snopf/snopf/src/avr/eeprom_access.c

// Copyright (c) 2020 Hajo Kortmann <hajo.kortmann@gmx.de>
// License: GNU GPL v2 (see License.txt)

#include "eeprom_access.h"

EEMEM struct EEPROM_LAYOUT eeprom_layout = {
    .dummy = 0x00,
    
    // Address 0x01
    .secret = {
        0x00, 0x00, 0x00, 0x00, 0x00, 0x00, 0x00, 0x00, 
        0x00, 0x00, 0x00, 0x00, 0x00, 0x00, 0x00, 0x00,
        0x00, 0x00, 0x00, 0x00, 0x00, 0x00, 0x00, 0x00, 
        0x00, 0x00, 0x00, 0x00, 0x00, 0x00, 0x00, 0x00},
    
    // Address 0x21
    .sha256_k = {
    0x428a2f98, 0x71374491, 0xb5c0fbcf, 0xe9b5dba5, 0x3956c25b, 0x59f111f1,
    0x923f82a4, 0xab1c5ed5, 0xd807aa98, 0x12835b01, 0x243185be, 0x550c7dc3,
    0x72be5d74, 0x80deb1fe, 0x9bdc06a7, 0xc19bf174, 0xe49b69c1, 0xefbe4786,
    0x0fc19dc6, 0x240ca1cc, 0x2de92c6f, 0x4a7484aa, 0x5cb0a9dc, 0x76f988da,
    0x983e5152, 0xa831c66d, 0xb00327c8, 0xbf597fc7, 0xc6e00bf3, 0xd5a79147,
    0x06ca6351, 0x14292967, 0x27b70a85, 0x2e1b2138, 0x4d2c6dfc, 0x53380d13,
    0x650a7354, 0x766a0abb, 0x81c2c92e, 0x92722c85, 0xa2bfe8a1, 0xa81a664b,
    0xc24b8b70, 0xc76c51a3, 0xd192e819, 0xd6990624, 0xf40e3585, 0x106aa070,
    0x19a4c116, 0x1e376c08, 0x2748774c, 0x34b0bcb5, 0x391c0cb3, 0x4ed8aa4a,
    0x5b9cca4f, 0x682e6ff3, 0x748f82ee, 0x78a5636f, 0x84c87814, 0x8cc70208,
    0x90befffa, 0xa4506ceb, 0xbef9a3f7, 0xc67178f2},
    
    // Address 0x121
    .sha256_h0 = {
        0x6a09e667, 0xbb67ae85, 0x3c6ef372, 0xa54ff53a,
        0x510e527f, 0x9b05688c, 0x1f83d9ab, 0x5be0cd19},

    // Address 0x141, begin of unprotected space
    .kb_delay = 20,
     
    // Address 0x142
    // Keycodes, first byte modifier, second byte key
    .keycodes = {
        // a..r
        {0x00, 0x04}, {0x00, 0x05}, {0x00, 0x06},
        {0x00, 0x07}, {0x00, 0x08}, {0x00, 0x09},
        {0x00, 0x0a}, {0x00, 0x0b}, {0x00, 0x0c},
        {0x00, 0x0d}, {0x00, 0x0e}, {0x00, 0x0f},
        {0x00, 0x10}, {0x00, 0x11}, {0x00, 0x12},
        {0x00, 0x13}, {0x00, 0x14}, {0x00, 0x15},
        // A..R
        {0x02, 0x04}, {0x02, 0x05}, {0x02, 0x06},
        {0x02, 0x07}, {0x02, 0x08}, {0x02, 0x09},
        {0x02, 0x0a}, {0x02, 0x0b}, {0x02, 0x0c},
        {0x02, 0x0d}, {0x02, 0x0e}, {0x02, 0x0f},
        {0x02, 0x10}, {0x02, 0x11}, {0x02, 0x12},
        {0x02, 0x13}, {0x02, 0x14}, {0x02, 0x15},
        // 0..9
        {0x00, 0x27}, {0x00, 0x1e}, {0x00, 0x1f},
        {0x00, 0x20}, {0x00, 0x21}, {0x00, 0x22},
        {0x00, 0x23}, {0x00, 0x24}, {0x00, 0x25},
        {0x00, 0x26},
        // -, @, ! 
        {0x00, 0x2d}, {0x02, 0x1f}, {0x02, 0x1e},
        // ?, $, *
        {0x02, 0x38}, {0x02, 0x21}, {0x02, 0x25},
        // +, =, &
        {0x02, 0x2e}, {0x00, 0x2e}, {0x02, 0x24},
        // #, [, ]
        {0x02, 0x20}, {0x00, 0x2f}, {0x00, 0x30},
        // (, ), .
        {0x02, 0x26}, {0x02, 0x27}, {0x00, 0x37},
        // :, >, <
        {0x02, 0x33}, {0x02, 0x36}, {0x02, 0x37}
    }
};

void ee_access_set_secret(const uint8_t secret[32])
{
    eeprom_update_block(secret, eeprom_layout.secret, 32);
}

void ee_access_set_keyboard_delay(uint8_t delay)
{
    eeprom_update_byte(&eeprom_layout.kb_delay, delay);
}

void ee_access_set_keyboard_codes(const uint8_t keyboard_codes[128])
{
    eeprom_update_block(keyboard_codes, (uint8_t*)eeprom_layout.keycodes, 128);
}

int8_t ee_access_get_key_modifier(uint8_t index, uint8_t* modifier)
{
    if (index >= 64) {
        return 0;
    }
    *modifier = eeprom_read_byte(&(eeprom_layout.keycodes[index][0]));
    return 1;
}

int8_t ee_access_get_key_code(uint8_t index, uint8_t* keycode)
{
    if (index >= 64) {
        return 0;
    }
    *keycode = eeprom_read_byte(&(eeprom_layout.keycodes[index][1]));
    return 1;
}
