snopf/snopf/src/host/pc/resources_rc.py

# Resource object code (Python 3)
# Created by: object code
# Created by: The Resource Compiler for Qt version 5.15.0
# WARNING! All changes made in this file will be lost!

from PySide2 import QtCore

qt_resource_data = b"\
\x00\x00\x09\xb5\
\x00\
\x00\x22\x03x\x9c\xcdZYo\x1b\xc9\x11~\xcf\xaf\xe8\
0/6\xc0\xa3\xefC\x90v\x11\xd3^\xc3\x80\x9c5\
b;\xc1\xfa\xc5\xa0\xc9\xb1\xc4,/p\xa8#\xff>\
_U\xf7\x0cG\x8a\xec\x95L)\xc8\x03\xd5U\xdd\xd5\
U\xd5_\xd5\xd4T\x0ft\xfc\xf3\xf5r!.\xabm\
=_\xafNzj({\xa2ZM\xd7\xb3\xf9\xea\xec\
\xa4\xf7\xf1\xc3/\x83\xd8\xfb\xf9\xa7?\x1d\xff\xf9\xe5\xaf\
\xe3\x0f\xbf\xbd{%\xea\xcb3\xf1\xee\xe3\x8b\xd37c\
\xd1\x1b\x8cF\xff4\xe3\xd1\xe8\xe5\x87\x97\xe2\xfd?^\
\x0b5T\xa3\xd1\xab\xbf\xf5D\xef|\xb7\xdb\x1c\x8dF\
WWW\xc3+3\x5co\xcfF\xaf\xb7\x93\xcd\xf9|\
Z\x8f 8\x22Al\x1aA\x99R\xc3\xd9n\xd6\x83\
\x09\xd2\xdcqD\xf7\xc4\xd5|\xb6;?\xe9%;\x0c\
f\xb9\xec\x89\xf3j~v\xbe\xebL\x5c\xce\xab\xab\x17\
\xeb\xeb\x93\x9e\x0b\xde\x0a%\x95\xb2\x22\xd9`\xf8OO\
l\xb6U]m/\xab\xbf\xd6\x9bj\xba\xfb\xfbd7\
_\x9f\xf4\xae\xdf\xceg\xbf\xe1\xd7\x13_\xe7\x8b\xc5`\
{\xb1\xa8Nz\xd5e\xb5Z\xcf0W\xef\xb6\xeb\xdf\
\xabA\xb1\xac\xe3Pk\xdd\xce.\xe6\xab\xea_\xeb9\
\xdc\xdb\xae/V\x90\x06v\xab\xfa\xe4\x8e\xd3j)%\
\x9d\xae\x88\x1c\xad\xd7\xebV\x0c3\xc3\xf5\x06\xf6\xbe~\
\x9dO+\x16\x87\xe4\xa8\xba\xde\xac\xb7\xbbf\xc35l\
\xfd~\x97f\x95R\x1a\xf1j#\xca\xa7\x5c\xed\xe8t\
\xabvG}\xb1\x1aN\xd7\xcb\x11\x8b\x8c\xea\xddd\x9b\
\xcd\x8d\xba\xd2\x8d\x86z9_|\xe3\x14j\xf4\xfe\xed\
\x9bS-G\x8d\xecd5_\x9e\xf4.\xb6\xab\xa3\xf5\
\xa4\x9e\xd7G\xab\xc9\xb2\xaa\x8fv\xd3#:\xd2l=\
\xbdXB\xfb\xd1^\x96\x0d\x1dq^a\xf2\xa8\xdeL\
\xa6\xc0\xbb\x89\x0c\xe2.\x8eg\xd5\xd7ZL\x17\x93\x1a\
P\x8e\x17\xf3\xcd\xbb\xc9\xee\xfc5\x10\xde\xd0\xaa8\x9e\
\x96)1\x9f\x95\x8d\xc5\xfd\xcf\xb4\xf2y\x83\xa5\x9eh\
\x84>\xae\xe6;\xa8\xb9\x80\xf6\xf7d\xea\xd7\xd5\xc7\x9a\
\xad@\xd1\x16I J\xb2\xf4\xc4\xbf\x91d\x940\x9d\
4\xa3\x9c\xd9\xe7\x18\xb8\x11;0j\x94\xdf\xd7\x9d\xcf\
\xf5\xf9\x96\x03\xf40\xaf\xc8|\xf6J\x9b\x8eW\xceu\
\xbd\x02\xf7\xdf^\x1d\x8f\x08\xc3\xdbX~\xa8\xaew\xef\
\xcf'\x9b\xea\xcdjV]g0\xcf\x04R\xf1\xa8^\
\xccg\x88\xc2|\xa6z\xcc\xcfg\xc8\xedzG3\x06\
\xe7\xb2\xf89\xfc<~\x01\xbf\x88_\xc2OI\xfa\xa3\
\xe8\x8ff/\xee\xb6\xfbj\xf9\xa5\x9a\xcd\xaa\xd9\x8b\x8b\
\xc5\xa2\xda\x8d\xcf'\xdb\xba1N\x98}\xe1\xe9\xc1\x14\
\xf3\x83]\xb5\xdc,&\xbbj\xe0\x82q\xbe'v\xdb\
\xc9\xaa\xfe\xba\xde\x22\xc5\xea\xe9dQ=\x93C<I\
6F\x1d\x95v\xfd\xc1\x0d\xf6yA\x90 \x17P\xfc\
V\xb8(\xfb\x08\xa9\x12\xa7B)o\xfa.(\x9e\x93\
b`[\x86\x05>5(\x9e\xdd\xc73{\xb0g\x11\
fud\xbfL\xc84S\x12+\xb2Y\xbd\xbfS\xc8\
\x11{8\x5c*X\x18?\x15^\xea~0\x89ye\
\xa3\x12\xca:\xdf\xceH\xf1I@\xd6\xb8\xc8S\xa7\xc2\
\xc8\xd4W\xc6z\xe1]\xcaR\xcd\xda\x83\x0e`\xf4\xc1\
\x07\xd0R\xb9\xe2\x94\xd2\xc1\xc3\xd5\xa0\x08S\xa5\xbd\xec\
;k\xd8\xfffL\xc6\xe7\x05\x22H.\x1fU7\x87\
n\x95=\xe4\x14R\x86\x83O!\xfb\x03-\xc6b@\
\x1e\x89\x81\xf2}\x1d\xc4\x00\xfbL \xb0\x11\x09\xe7\x03\
\xd6\xb5\xd7\xfd\xa8\x8d\xd0p39]F\x9b\xc7\x90\x84\
\xd6\xb1\x9f\x12\xe6\x9d\xcb\xa3\xb7y\x040)I\xa1c\
\xea\xa7\x18\x84Q\x80 )a\x8c\xc2\x98`\x01\x00\xa0\
\xe6\x90\xb1\x98\xa7lBB\xd8(B\xd0X\xb2ID\
\xe3Ah+\x22\xf0\xe3\x99\xb1\x88\x10V\x12x%I\
\x84v\x22i\x12\x97\x1eK0\x09\xf7\xa3q\xfd\xe8\x0d\
\xf4\xc8~\x88V\x04\x8f\x84\x89\xe0\xe1BP^\xb8\x84\
\xf0`\xfe\x14\x12\xb6\xafq\xb81S*!B\xce\xf4\
\x95\x87\x0f\x0a\xda9\xc4A\xd3\x93C\xa6)z8\x91\
OP\x874\x84\x974XE\x83\x83-\x15\xa2\xb0.\
\xf4q\x1eJ\x0d\x001\xc0\xca\x18y\xad\xfb\x03\x852\
\xa6\xa0t\x80\xd0Cg\x1e\x8d\xccc\xca\xeb\x917@\
\xc6S(\xfa\x03\xc0M\x83\xc9\x03\xfc\x1c\xd0~\x93C\
\xf7\xb0|9\xbc\x96\xe8\x08\x19CX\xa9\xa8\x99\xa2\xe3\
\x18$?\x90s@@\x03J\x00\x809\xaca\xb0\xa8\
|\x18\x1c\xc2\x86\xdc\xf0\x00\x1e\xfb\x80\x1a\x15I\xc4\x19\
\xfb).\xc0L[\x99\xc7dx4H\xa9`\x81\x8e\
\xf5}\xcfq2\x90t2\xc2\xb6\x09\xa1o\xad\x15&\
a\xc4K\xc1B\xd6*\xd9\x94^\xb8\xc4\x88sM!\
d\x119\xe4\x90\x22o\xb5N\x0d\x15TC!\xe5\xb0\
'\x16J\xc6\xc0\x0f5\xe8\xe4\x1d)bR\xa3\xd8h\
8\x8f\x94\xa3g\x19\x0f\x04G\xd8\x22\xae\x96\x9e\x11\x93\
\x10\x11\x8f\xd4\x8e\x8cK\x83\xd4\xfd#\x94|H\x87\x17\
{eP\x84\xc6\xc2\x1b\x8d\xd1\xe2\xb9\xc3cj\x22\xe5\
\xb3\xe2\xc7Q#\xaf\x91\xed\x8c\x1b\x8d\x8e\x1eSM\x98\
\x9b\xfc\xb8\x02;\x96\x97H5\xda\x0f\x8c$\xab\x03B\
\x96\xf53\x91R\x99\xc1\xba\xcfBJ[\x97\xf7\xa1*\
\x1b\xd6\xa4\xac\x0cP\xad3A\xb6\x98\xb0x\xe4Y\x86\
\xbc\xc9\xdb\xe0\x1ekrY\xb5,'\xb9?|Q\xeb\
\xc3_K\x94mxz\xa9\xe4\x05\xc3\x94\xc6\x1b\xc7\xa2\
n(\xa4\xaf3\x8e:}\xd4\x0dO\x09\xef\x91\xd4\x18\
\x02\x0eL\x03\x0a\x07-F\x97X8\x11\xc0\xd8\x9c\xbc\
ae)&VO\xa3U)\x8f\xe8\x09h\xddQ=\
D\x02;\xe4\x17\xed\xf72\xb2>\x1e\xa1\x9eF\x8f\xa2\
\xe8\x10\x182\xee\x10\x0er\xc6B\x9e\x9c\xb3Z\xb2\xb3\
\x8d\xfb\x0fAM\xa9\x83QC\x87c]\xca\x1d\x86c\
\x92\x09\x8fr\x8c\xa52\xd0\xf4\xfd\xfd\xf2\xca\xd9\xf8\x08\
]\x06\x12\xdb\xd2\xf3@T\x92\x88\x84\xa1\x17\x06\xea\x0e\
A\xa5\x14|\xb2x\x94\xe9M\x0c\x90\xa9\xda\xa3\xce\x06\
\xef2\x91PW\x98P\xd2\x87,\x84\x947y\x1f\xaa\
B\xca\xaap\xd6\xc0\xca\x99 {L\xa0\xab\xceB\xd6\
\x84\xbc\xcf\xe8\xa2J\x03\x12VN/:\xb2\x86\x91\xcd\
c$\x7fh\x9d\x1c\xa4\x0d\xe41k\x08&\xab,g\
\xba\x81\xe5\xb7\xbb\xf0\xb6#\x9e\xef\x96\x93M\x9d{\xe7\
\xb3F\xe2=u\xe3\x9d\x0b\xcfYF0\x07f\xba\xc6\
\xf5\x02\xf7\xce\xed\x80\xbau^i\x96\xb8}\xef\xea\xc8\
\x17\x8e\x01AOW\xb4\xc5\xb3\xbf\xdc}?)1\x12\
\x1d\x1f\xdeM\xce\xaaf\xb63\x8d+\xe4\x90\xae\x92t\
\x81\x1c\xce\xb6\x93\xab\xf9\xeal8\xbe\xa8w\xeb%\xdf\
,\xda-{\x9f\xcc~\xae\x5cn\x8a\xae\x17tg\xc6\
~\x5c\xd8\x9b\x1b\xf5Io\xb5^U\xf9&\xde\xd0\xdf\
\xbd\xa0\xd9\x1b\x174\x9b\xd1/\xb68\xe3\xb2\xa6\xed\xd9\
\x97gx\x93QYx~\xdbV\xceI\xe9$52\
h\x0d(/\x8dB\xaadN9\x85\xe6Ei\x95L\
C\xdb\xe8dC\x07'C#\x9f\x1cu\x94Y\x13\xd3\
hqL!]T\xb6Hg\x92\x95d\x92ug\xd9\
l\xb2\xe3\x0c\xb5\xdaY\x8a\xd9\xd3.\xc3m8\xdc\xc8\
\xa6\xf9\xfd\xd8\xe1>}\x0b\x8c|\xec\x06\x84\x0c\x8dF\
e\xd0:<\xbf\xfd\xc1\x03\x0d\xca\xb7\xbfv\xfc\x9f#\
\xd79\x7f\xa9m\xb7\xc9C\xd2\xda\x1e\x9e\xd6\xc9\x9a\x98\
\xd3\x1a\x855\xb6i\xad\x15\xbd3\x9b\xb4f\xee\x11\x22\
\xe9\xef\x11IK\xc5\xd3[G\xed\x9c\x92\x89\xaa2s\
\xe8\xd7<\xd1!\x86\x86\x0e\x80\xbe\xa5\xbdS\x8d|H\
t\x87\xca\x9a\x0a\xcde\x9a\xe9\x14\xd0\x87e\xf1B\x92\
\x96Lf\xe5Y8\x1b\xed\xb8\xf3\xc4\xb1t\x87\xc7\x12\
\x9e\x1b\x9f\x83i\x92\x0a\xfb\x1a\xa5S'\x96\xc8\xdc\xef\
\x97\xa8\xdb\xd1\xbb\xabH\xf9\xe0==\xebd\xb1p\x85\
&\xcb\x14\x08\xdcon\xd0Ef\xbf\xfb\x89\xf1\xf4\x8f\
\x81'\xee\x8b-\x9e\xfb\x87\x03\x8d\xd8\x1e\xcf\xe0\xcdA\
p&\xfa\xf4b\xd1\x0d0\x9c\xcc\x911\xba\xa4$w\
\x93\xb6>\xcavG\x97\xa6\xddO\x0cgx\x0c8\xb5\
\xd4\x19N'\xbdl\xe1\xc4\x19\xe3\x1eOo\xbeYj\
\xee\x85'l\xe0\xc2i\x02\x7f\xd7*\x1c\xac\x09j\xcd\
\xd2-\xda'\xd7\xcati\xda\xfd\xc4x\xc6G(\xdd\
\xb8u\xde\xf1\xb4Sj\xec\xe1t\xfe\x0f\x1a\x92\xef\xc2\
I&\x90_\x8a\xb333\xe5\x99v%9[\xda\xe2\
\xca\xd2\xc8wH\xf5\xc0\xd4\xdc\xb7\x9c?\x8c\xf1\x1e\xe4\
\xd4\x99\xfcq\x94}\xa9\xa9\xda\xf8\xfd'p\xed\xbb(\
'\x17\xba(\xff`Q5Fe\x9c\xbd/L&\xc9\
0\xdf\x13\xccM\x9aE\xba{o\xb6[{xo\xd2\
\x07A\xaa\xe4\xa3b\x8a\x04\xb1]L;\x85U\xc9\x10\
\x0f\x015\x19\xfaz@\x06\xd0I$\xfa\x00\x99\x99\x8c\
)\x0a\x81iI4p\xa7-\xd6\xb8\x9d\x8f\x1b\xc6J\
U\xb6j\x9bTQ\xc9$\x7fQ\xa2\x8f\x94\xcc\xe5o\
J\x0dG\xe1\xb1ewC\x93\xda\xd3\x86c\x8b\xe3=\
G7\xc4\xbc\x9f=,\x9a\x99>\xed\x9e\x83\x9a\xed\xe2\
sY\xdb3\xdc\x887\x86S\xc7\x18s\xf7\xc9\x8c\xa7\
\x7f\x1e\x95z\x8c\xe4\xb1\xa6\xbcE4.\xf7m\xf2x\
zU\xb7U\xcf\xa8?H\x9d\xef\xdc\xc3\x92\xd3x\xa0\
H9%\x82\x0d\xbe0d\x98\x22I\x1f\x95\x0b\xe9\xf9\
y\xcdL\xd0\x9a\xe53\x83\x06\xa7l\x8d\x88|Q\x19\
9\x09R\x0a\xa90\xd4\xe2Jm\x0aG\x9dg,\x9b\
[Z\xeb\xdcg1G\x06\xc7{N\xbbv?;\x98\
\x15k\xfe\xfc\xd89\x05\xa7M\xf6\xab\xac\xed\x19N\x9b\
\xa2/\xbb\xd7\xe5\xfe\x17\x05E?BNP#\xf4\xb4\
I\xa1\xa87h\xb3\x02\xf6\xda\xb4`\xdbm4R'\
1\x1a.gF\xcbqtS\x9b\x1b\x8d\xe6\x82\xbe\xb2\
\xdd\xecPn\x9f\x1d\xe8Q\xda\xech\xe8\x9c\x1d\x85+\
\xd9\xd1p\xe4O\xd9\xcf~\x16\xcd9\x05\xba\xe7\xc99\
\x90:\x09\xd2\xe5raq\xdd\x0c\xe9p\x0f+,-\
\xd5\x10\xcd\x07\xbf\xf2\xad\x0a\x7f\x8f\xe9\x1f\x0f~\xfa\x0f\
9\xdbl\x0a\
"

qt_resource_name = b"\
\x00\x04\
\x00\x06\xfa^\
\x00i\
\x00c\x00o\x00n\
\x00\x08\
\x0aaW'\
\x00i\
\x00c\x00o\x00n\x00.\x00s\x00v\x00g\
"

qt_resource_struct = b"\
\x00\x00\x00\x00\x00\x02\x00\x00\x00\x01\x00\x00\x00\x01\
\x00\x00\x00\x00\x00\x00\x00\x00\
\x00\x00\x00\x00\x00\x02\x00\x00\x00\x01\x00\x00\x00\x02\
\x00\x00\x00\x00\x00\x00\x00\x00\
\x00\x00\x00\x00\x00\x02\x00\x00\x00\x01\x00\x00\x00\x03\
\x00\x00\x00\x00\x00\x00\x00\x00\
\x00\x00\x00\x0e\x00\x01\x00\x00\x00\x01\x00\x00\x00\x00\
\x00\x00\x01o\xcf;\x0b\xd8\
"

def qInitResources():
    QtCore.qRegisterResourceData(0x03, qt_resource_struct, qt_resource_name, qt_resource_data)

def qCleanupResources():
    QtCore.qUnregisterResourceData(0x03, qt_resource_struct, qt_resource_name, qt_resource_data)

qInitResources()
