snopf/snopf/src/avr/eeprom_access.h

// Copyright (c) 2020 Hajo Kortmann <hajo.kortmann@gmx.de>
// License: GNU GPL v2 (see License.txt)

#ifndef __eeprom_access_h__
#define __eeprom_access_h__

#include <stdint.h>
#include <string.h>

#ifdef TEST_NO_MCU
    #define EEMEM
    #define eeprom_read_block(dst, src, count) (memcpy(dst, src, count))
    #define eeprom_update_block(src, dst, count) (memcpy(dst, src, count))
    #define eeprom_update_byte(dst, val) (memset(dst, val, 1))
    #define eeprom_read_byte(x) *(x)
    #define eeprom_read_dword(x) *(x)
#else
    #include <avr/eeprom.h>
#endif

struct EEPROM_LAYOUT {
    uint8_t dummy;
    uint8_t secret[32];
    uint32_t sha256_k[64];
    uint32_t sha256_h0[8];
    uint8_t kb_delay;
    uint8_t keycodes[64][2];
} __attribute__((packed));

extern EEMEM struct EEPROM_LAYOUT eeprom_layout;

// Set secret in eeprom to new secret
void ee_access_set_secret(const uint8_t secret[32]);

// Set new keyboard delay
void ee_access_set_keyboard_delay(uint8_t delay);

// Set new keyboard keycodes
void ee_access_set_keyboard_codes(const uint8_t keyboard_codes[128]);

// Get keyboard modifier for given key index
// Returns 0 if we try to access space outside the unprotected scope
int8_t ee_access_get_key_modifier(uint8_t index, uint8_t* modifier);

// Get keyboard keycode for given key index
// Returns 0 if we try to access space outside the unprotected scope
int8_t ee_access_get_key_code(uint8_t index, uint8_t* keycode);

#endif  //__eeprom_access_h__
